QWaveSystems/QWAVE_Raspberry-Pi-CM4-Altium-Library/CatsPi-Backflip-Board-using-CM4/CatPi_HAT_Flip_version-G01.png

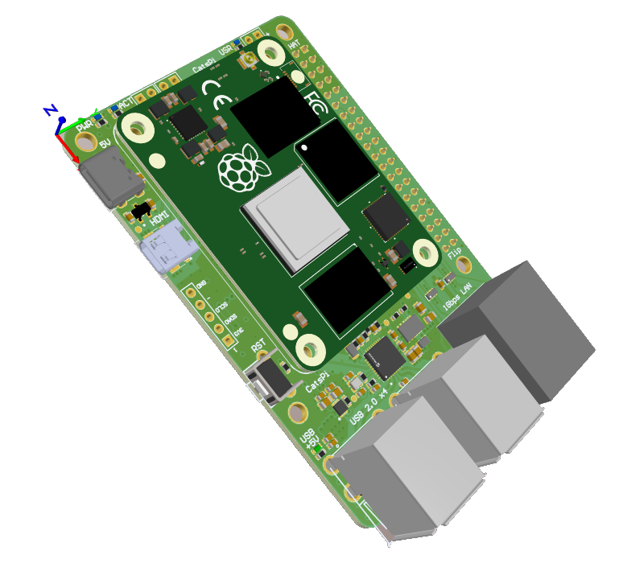
CatsPi-Backflip-Board-using-CM4/CatPi_HAT_Flip_version-G01.png
