QWaveSystems/QWAVE_Raspberry-Pi-CM4-Altium-Library/CatsPi-Dev-Board-using-CM4/2020-12-16_1-04-19.png

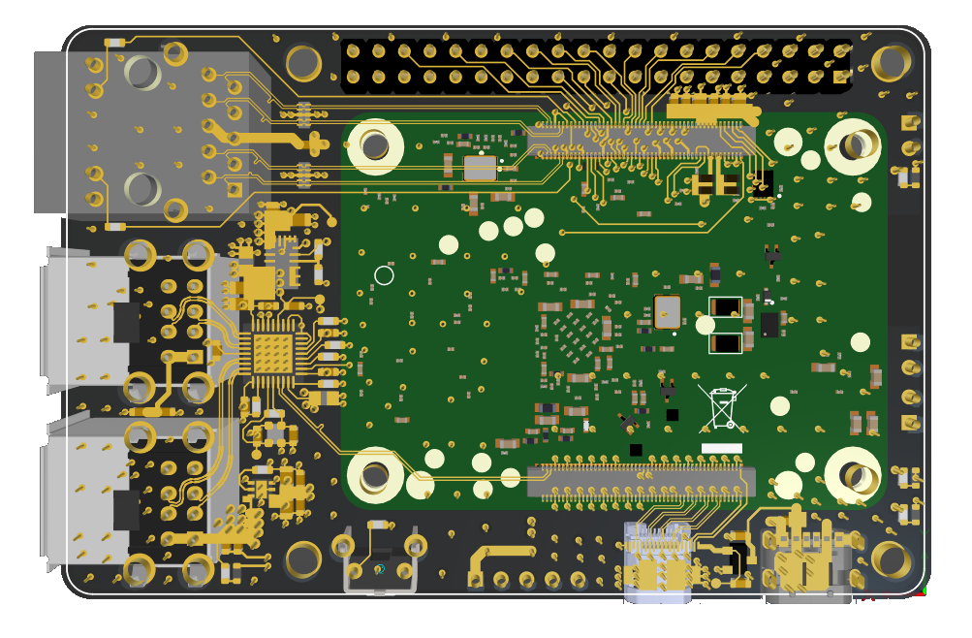
CatsPi-Dev-Board-using-CM4/2020-12-16_1-04-19.png
