QWaveSystems/QWAVE_Raspberry-Pi-CM4-Altium-Library/SCH_Snapshot-Picture/CatsEYE-Flasher_00.png

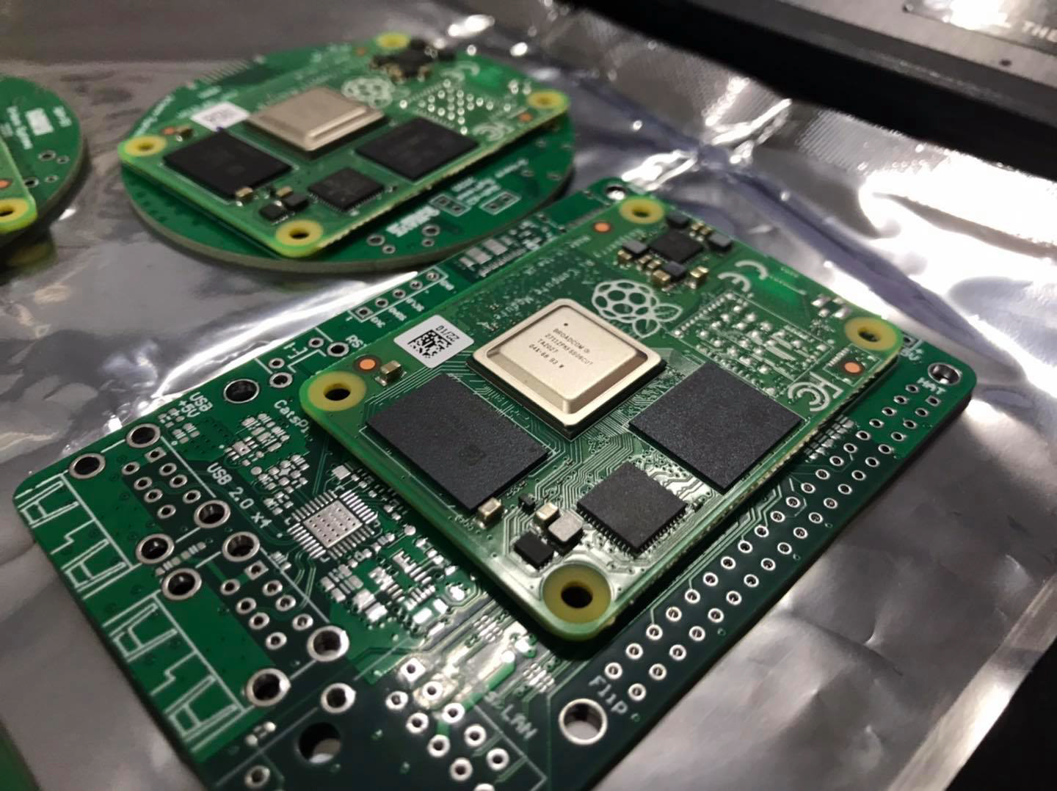
SCH_Snapshot-Picture/CatsEYE-Flasher_00.png
