QWaveSystems/QWAVE_Raspberry-Pi-CM4-Altium-Library/SCH_Snapshot-Picture/CM4_Page_09.jpg

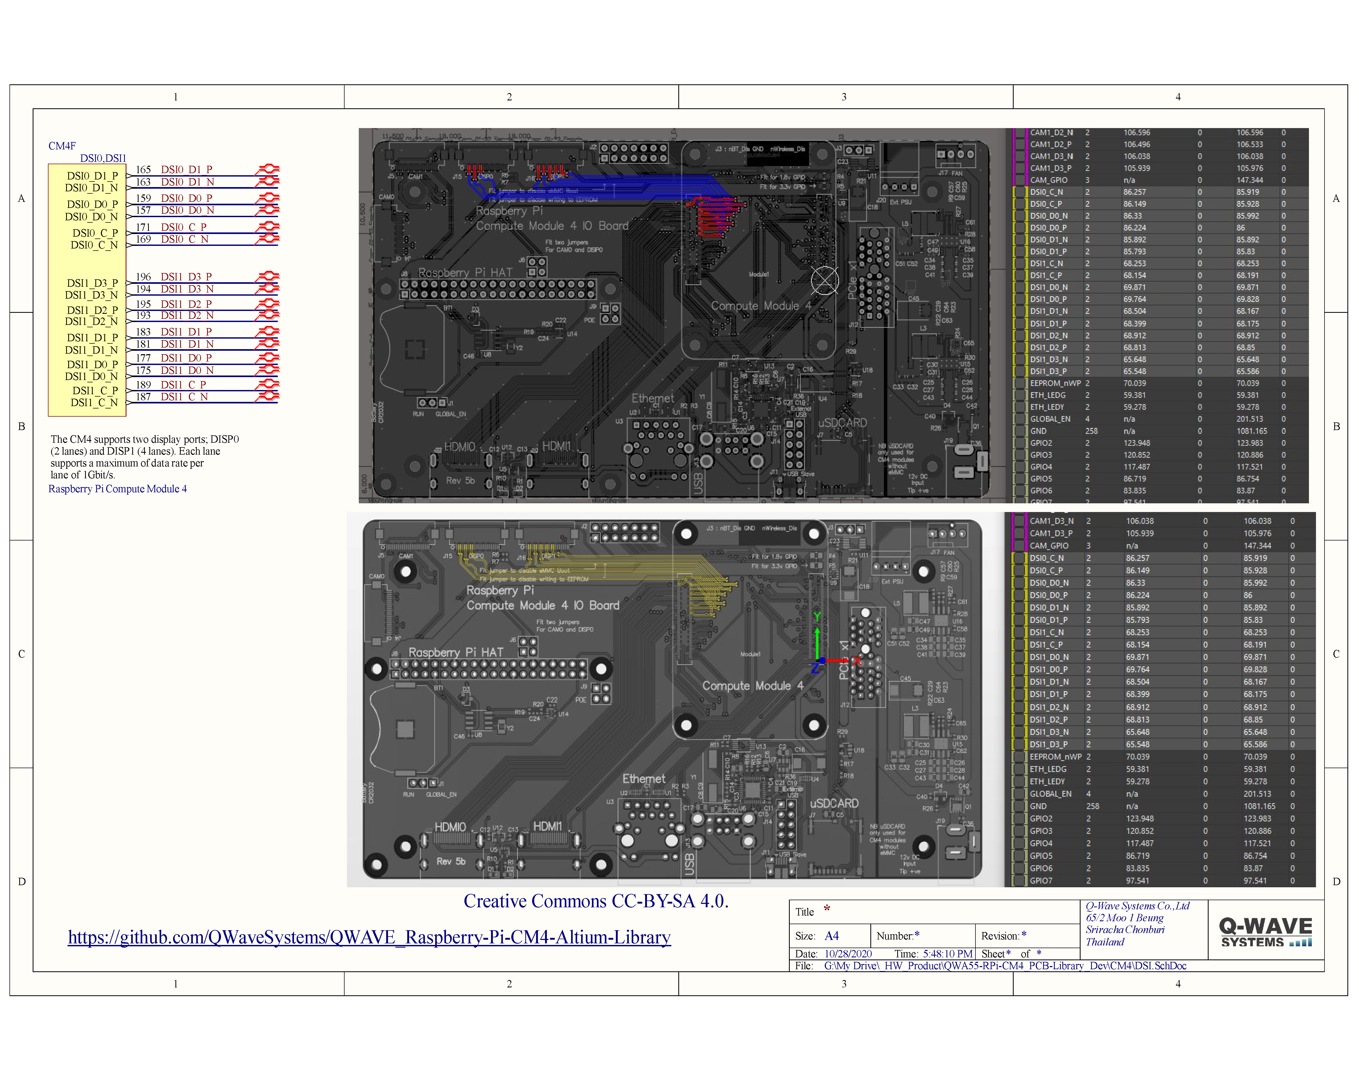
SCH_Snapshot-Picture/CM4_Page_09.jpg
