QWaveSystems/QWAVE_Raspberry-Pi-CM4-Altium-Library/SCH_Snapshot-Picture/Gateway_03.jpg

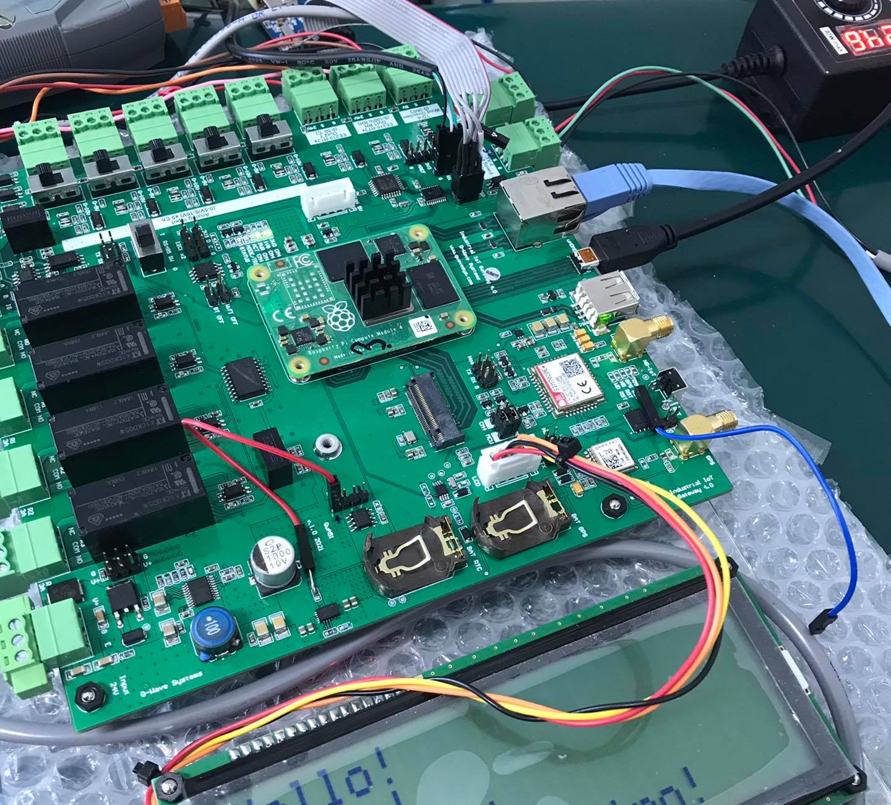
SCH_Snapshot-Picture/Gateway_03.jpg
