QWaveSystems/QWAVE_Raspberry-Pi-CM4-Altium-Library/SCH_Snapshot-Picture/SeaBOX_HDMI_Stick_05.png

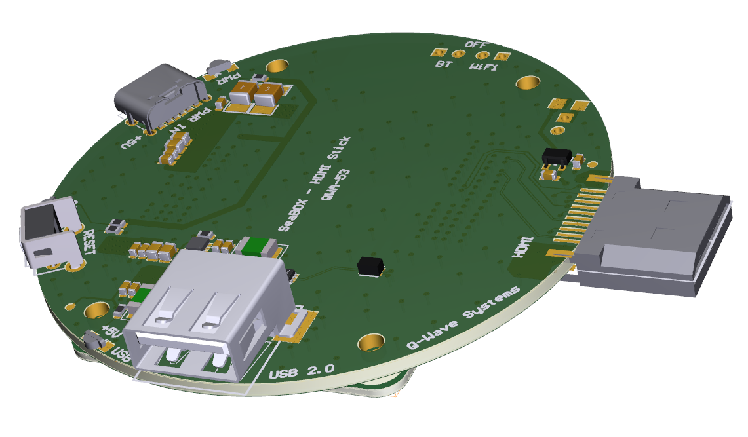
SCH_Snapshot-Picture/SeaBOX_HDMI_Stick_05.png
