QWaveSystems/QWAVE_Raspberry-Pi-CM4-Altium-Library/SeaBOX-HDMI-Stick-using-CM4/2021-01-11_9-55-34.png

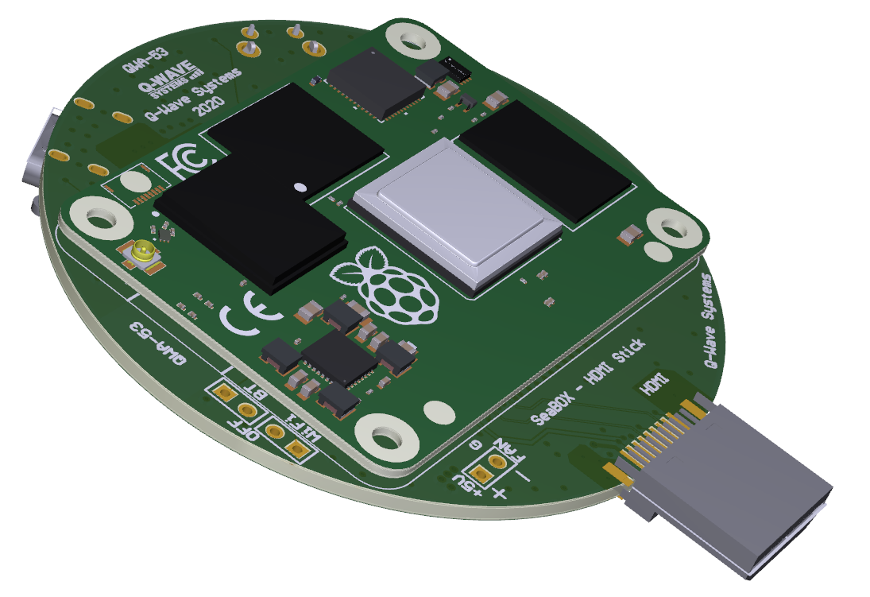
SeaBOX-HDMI-Stick-using-CM4/2021-01-11_9-55-34.png
