QWaveSystems/QWAVE_Raspberry-Pi-CM4-Altium-Library/SeaBOX-PoE-HDMI-Stick-using-CM4/2020-11-20_10-55-00.png

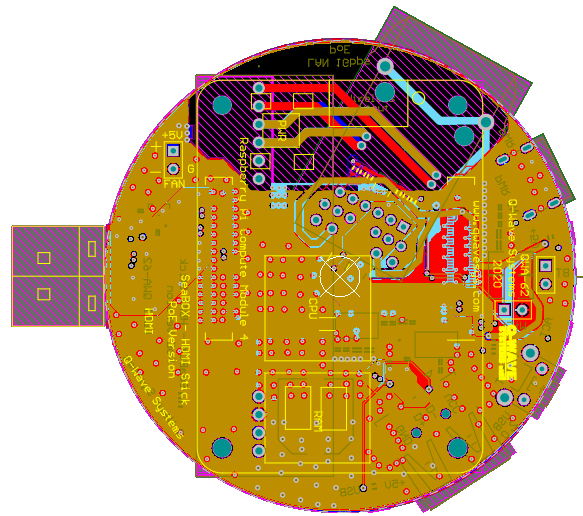
SeaBOX-PoE-HDMI-Stick-using-CM4/2020-11-20_10-55-00.png
