QWaveSystems/QWAVE_Raspberry-Pi-CM4-Altium-Library/SeaBOX-PoE-HDMI-Stick-using-CM4/SeaBox_PoE--G01.png

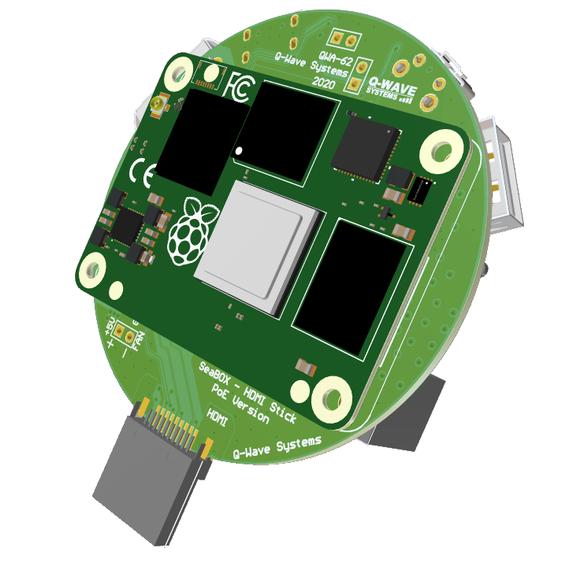
SeaBOX-PoE-HDMI-Stick-using-CM4/SeaBox_PoE--G01.png
